danielhood/shape/compression/schematics/rev01/compressor_poc.sch

## EAGLE design compression/schematics/rev01/compressor_poc.sch (2023-01-11)

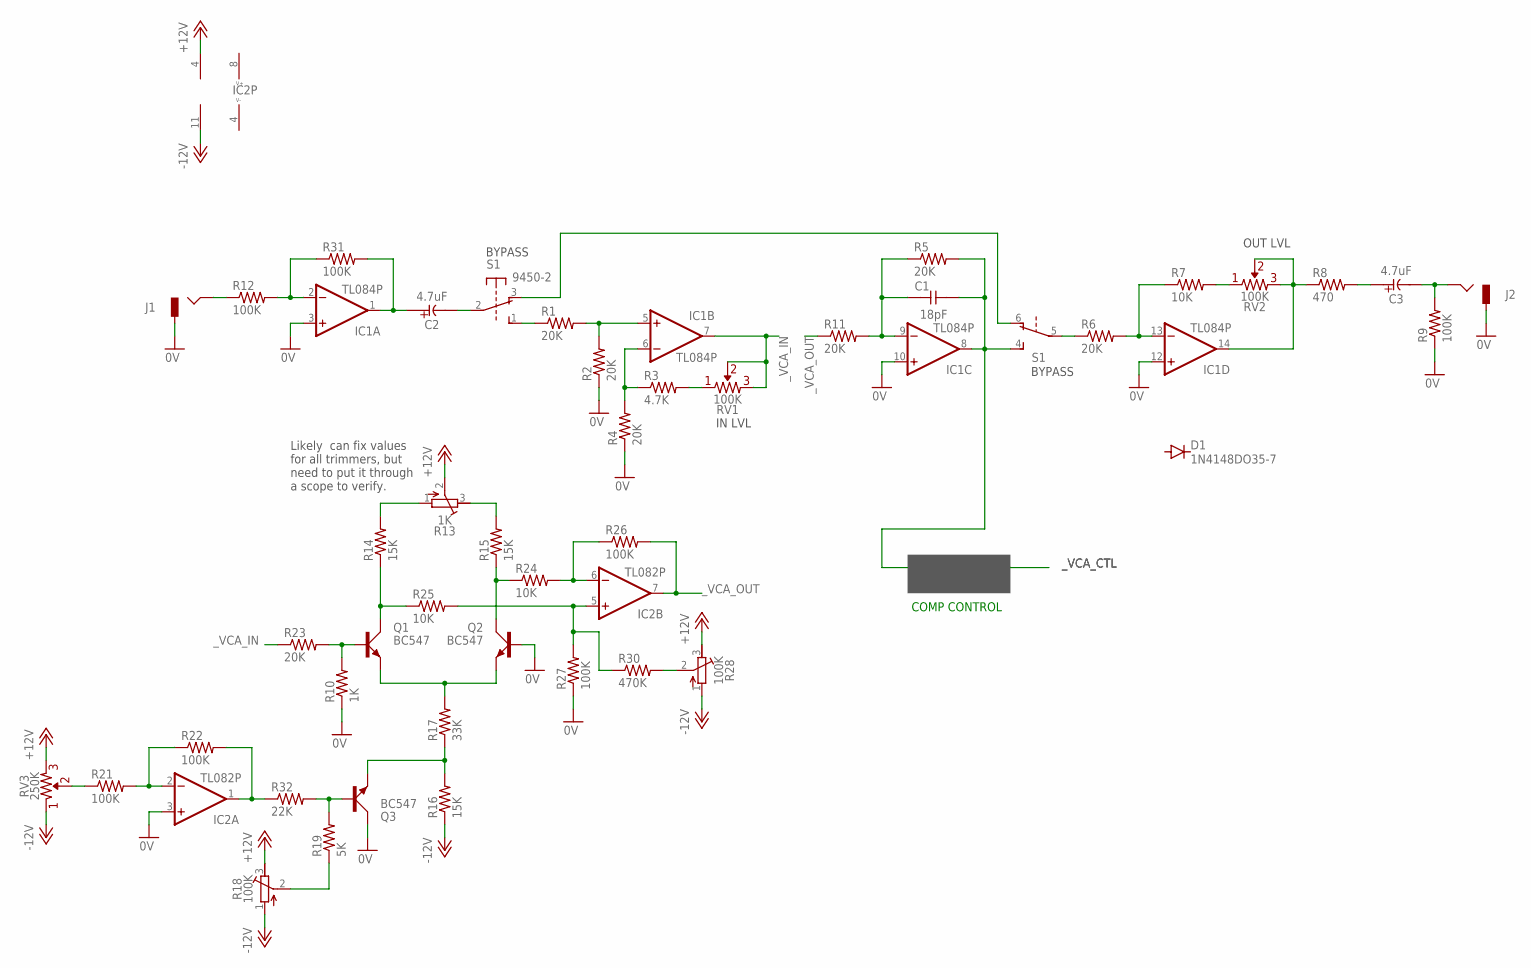
[picture p5: schematic compressor_poc.sch]

Parts:
C1: 18pF; C025-024X044
C2, C3: 4.7uF; E2-5
D1: 1N4148DO35-7; DO35-7
IC1: TL084P; DIL14
IC2: TL082P; DIL08
J1, J2: JACK-M
Q1, Q2, Q3: BC547; SOT54A
R1, R2, R4, R5, R6, R11, R23: 20K; 0204/7
R3: 4.7K; 0204/7
R7, R24, R25: 10K; 0204/7
R8: 470; 0204/7
R9, R12, R21, R22, R26, R27, R31: 100K; 0204/7
R10: 1K; 0204/7
R13: 1K; RTRIM3304W
R14, R15, R16: 15K; 0204/7
R17: 33K; 0204/7
R18, R28: 100K; RTRIM3304W
R19: 5K; 0204/7
R30: 470K; 0204/7
R32: 22K; 0204/7
RV1, RV2: 100K; R-VAR
RV3: 250K; R-VAR
S1: 9450-2

Connections:
0V: IC1.3 (+IN), IC1.10 (+IN), IC1.12 (+IN), IC2.3 (+IN), J1.GND, J2.GND, Q2.B, Q3.C, R2.1, R4.1, R9.1, R10.1, R27.1
+12V: IC1.4 (V+), R13.2 (S), R18.3 (A), R28.3 (A), RV3.R2 (2)
-12V: IC1.11 (V-), R16.1, R18.1 (E), R28.1 (E), RV3.R1 (1)
unnamed: R13.1 (E), R14.2
unnamed: IC1.5 (+IN), R1.2, R2.2
unnamed: R3.2, RV1.R1 (1)
unnamed: IC1.6 (-IN), R3.1, R4.2
unnamed: R1.1, S1.1 (S)
unnamed: C2.-, S1.2
unnamed: J1.HOT, R12.1
unnamed: C1.2, IC1.8 (OUT), R5.2, S1.4 (S)
unnamed: S1.3 (O), S1.6 (O)
unnamed: IC1.13 (-IN), R6.2, R7.1
unnamed: R7.2, RV2.R1 (1)
unnamed: IC1.14 (OUT), R8.1, RV2.R2 (2), RV2.VAR
unnamed: R6.1, S1.5
unnamed: C3.+, R8.2
unnamed: C3.-, J2.HOT, R9.2
unnamed: C2.+, IC1.1 (OUT), R31.2
unnamed: IC1.2 (-IN), R12.2, R31.1
unnamed: C1.1, IC1.9 (-IN), R5.1, R11.2
unnamed: R13.3 (A), R15.2
unnamed: Q2.C, R15.1, R24.1
unnamed: Q1.C, R14.1, R25.1
unnamed: Q1.E, Q2.E, R17.2
unnamed: Q3.E, R16.2, R17.1
unnamed: Q3.B, R19.2, R32.2
unnamed: IC2.1 (OUT), R22.2, R32.1
unnamed: R18.2 (S), R19.1
unnamed: IC2.2 (-IN), R21.2, R22.1
unnamed: R21.1, RV3.VAR
unnamed: Q1.B, R10.2, R23.2
unnamed: IC2.5 (+IN), R25.2, R27.2, R30.1
unnamed: R28.2 (S), R30.2
unnamed: IC2.6 (-IN), R24.2, R26.1
_VCA_IN: IC1.7 (OUT), R23.1, RV1.R2 (2), RV1.VAR
_VCA_OUT: IC2.7 (OUT), R11.1, R26.2

Notes on the sheet:
BYPASS
IN LVL
OUT LVL
COMP CONTROL
Likely can fix values for all trimmers, but need to put it through a scope to verify.
